zykrah/fuyu/marbastlib/3d/holyiot_18010_nRF52840.step

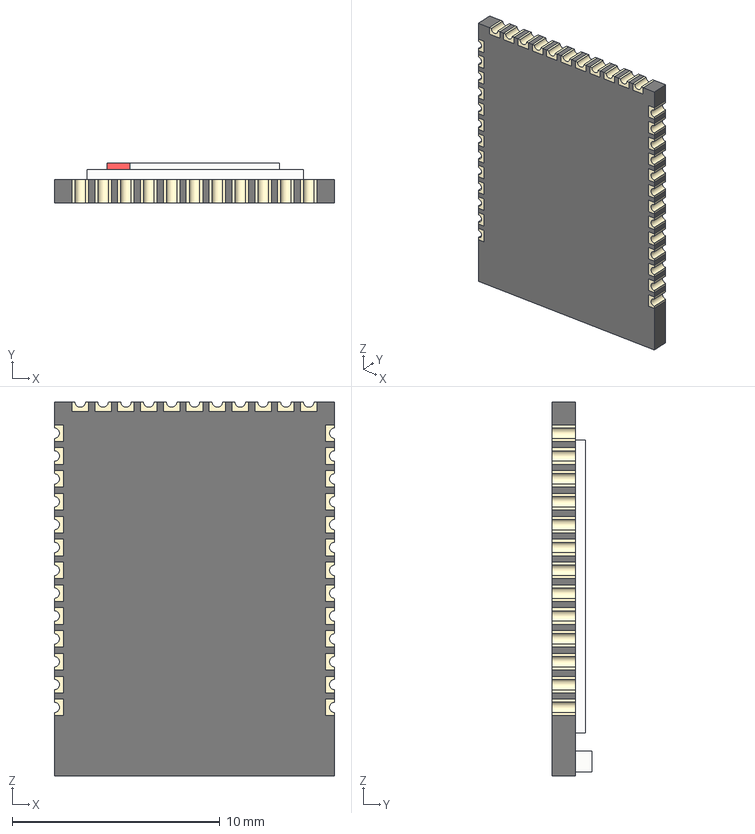
[picture p15: CAD file, 2022-04-11]
marbastlib/3d/holyiot_18010_nRF52840.step
13.5 x 1.92 x 18.0 mm
