zykrah/fuyu/marbastlib/3d/Switch_ESP3020.step

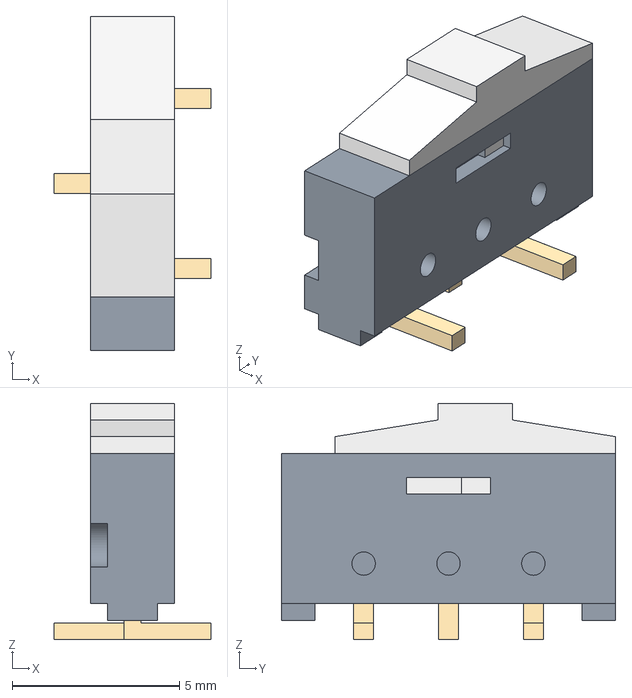
[picture p17: CAD file, 2022-04-11]
marbastlib/3d/Switch_ESP3020.step
4.70 x 10.0 x 7.08 mm
