zykrah/fuyu/marbastlib/3d/SW_SSSS213100.step

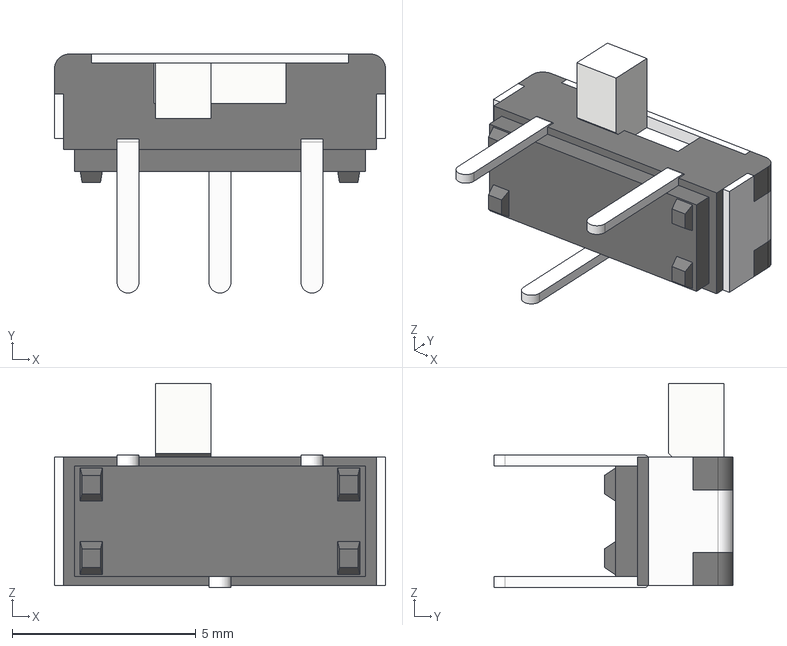
[picture p20: CAD file, 2022-04-11]
marbastlib/3d/SW_SSSS213100.step
9.00 x 6.50 x 5.55 mm
