zykrah/fuyu/marbastlib/3d/SW_SKHLLC.step

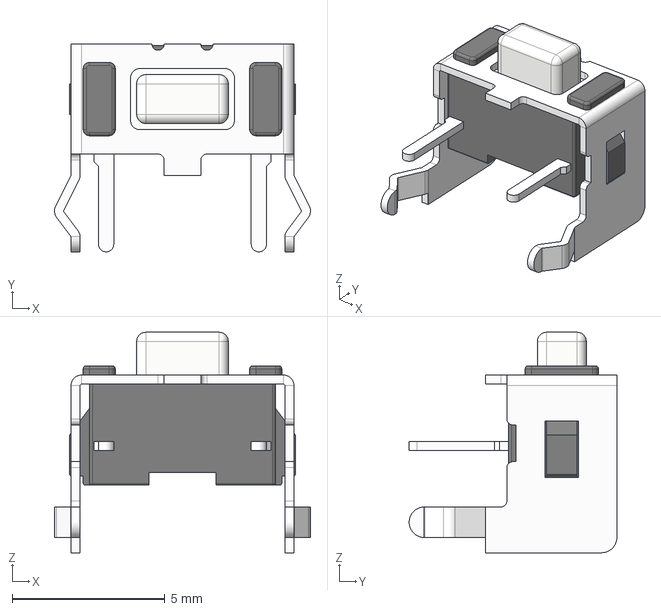
[picture p23: CAD file, 2022-04-11]
marbastlib/3d/SW_SKHLLC.step
8.38 x 6.80 x 7.22 mm
