zykrah/fuyu/marbastlib/3d/LED_SK6812MINI-E.step

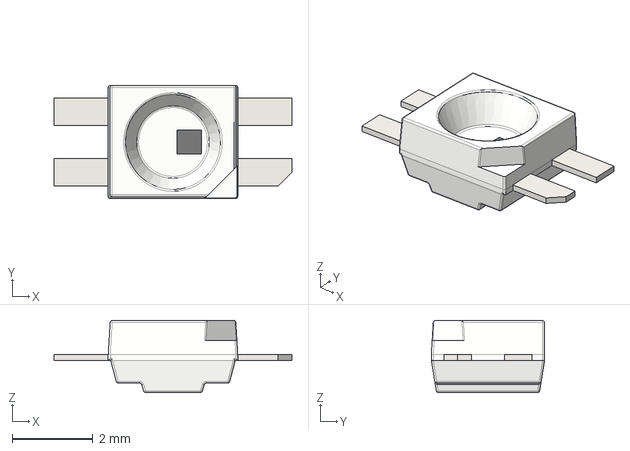
[picture p26: CAD file, 2022-04-11]
marbastlib/3d/LED_SK6812MINI-E.step
5.88 x 2.80 x 1.78 mm
