zykrah/fuyu/marbastlib/3d/ROT_EC11E.step

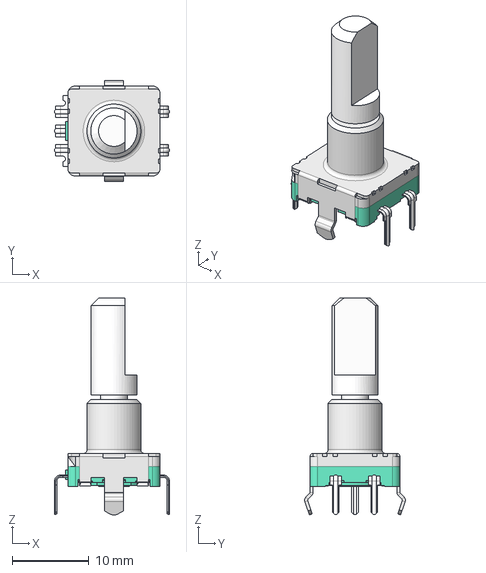
[picture p27: CAD file, 2022-04-11]
marbastlib/3d/ROT_EC11E.step
14.9 x 13.1 x 28.2 mm
